ubx/CAN-logger2/src/logger/wifi_web.h

#pragma once

#include <string>
#include "esp_http_server.h"

// Initializes WiFi as SoftAP
void wifi_init_softap();

// Starts webserver (returns handle)
httpd_handle_t start_webserver();

// Mount SD for WiFi file browsing
bool mount_sdcard();

// For idle timeout tracking
unsigned long get_last_web_activity();

void reset_web_activity();

const char* get_ip_address();
